vaizq/NutriDoser/Software/Sensei/src/wifi.hpp

#ifndef SERVER_HPP
#define SERVER_HPP

#include "esp_event.h"
#include "esp_log.h"
#include "esp_system.h"
#include "esp_wifi.h"
#include "freertos/FreeRTOS.h"
#include "freertos/event_groups.h"
#include "freertos/task.h"
#include "nvs_flash.h"
#include "wifi_provisioning/manager.h"
#include "wifi_provisioning/scheme_softap.h"
#include <string.h>

#include "lwip/err.h"
#include "lwip/sys.h"

#define ESP_WIFI_SAE_MODE WPA3_SAE_PWE_HUNT_AND_PECK
#define EXAMPLE_H2E_IDENTIFIER ""
#define ESP_WIFI_SCAN_AUTH_MODE_THRESHOLD WIFI_AUTH_WPA2_PSK
#define WIFI_MAXIMUM_RETRY 5

/* FreeRTOS event group to signal when we are connected*/
static EventGroupHandle_t wifi_event_group;

/* The event group allows multiple bits for each event, but we only care about
 * two events:
 * - we are connected to the AP with an IP
 * - we failed to connect after the maximum amount of retries */
#define WIFI_CONNECTED_BIT BIT0
#define WIFI_FAIL_BIT BIT1

static const char *TAG = "wifi station";

static int s_retry_num = 0;

static void event_handler(void *arg, esp_event_base_t event_base,
                          int32_t event_id, void *event_data) {
  if (event_base == WIFI_PROV_EVENT) {
    switch (event_id) {
    case WIFI_PROV_START:
      ESP_LOGI(TAG, "Provisioning started");
      break;
    case WIFI_PROV_CRED_RECV: {
      wifi_sta_config_t *wifi_sta_cfg = (wifi_sta_config_t *)event_data;
      ESP_LOGI(TAG,
               "Received Wi-Fi credentials"
               "\n\tSSID     : %s\n\tPassword : %s",
               (const char *)wifi_sta_cfg->ssid,
               (const char *)wifi_sta_cfg->password);
      break;
    }
    case WIFI_PROV_CRED_FAIL: {
      wifi_prov_sta_fail_reason_t *reason =
          (wifi_prov_sta_fail_reason_t *)event_data;
      ESP_LOGE(TAG,
               "Provisioning failed!\n\tReason : %s"
               "\n\tPlease reset to factory and retry provisioning",
               (*reason == WIFI_PROV_STA_AUTH_ERROR)
                   ? "Wi-Fi station authentication failed"
                   : "Wi-Fi access-point not found");
      break;
    }
    case WIFI_PROV_CRED_SUCCESS:
      ESP_LOGI(TAG, "provisioning successful");
      break;
    case WIFI_PROV_END:
      /* De-initialize manager once provisioning is finished */
      wifi_prov_mgr_deinit();
      break;
    default:
      break;
    }
  } else if (event_base == WIFI_EVENT) {
    if (event_id == WIFI_EVENT_STA_START) {
      esp_wifi_connect();
    } else if (event_id == WIFI_EVENT_STA_DISCONNECTED) {
      if (s_retry_num < WIFI_MAXIMUM_RETRY) {
        esp_wifi_connect();
        s_retry_num++;
        ESP_LOGI(TAG, "retry to connect to the AP");
      } else {
        xEventGroupSetBits(wifi_event_group, WIFI_FAIL_BIT);
      }
      ESP_LOGI(TAG, "connect to the AP fail");
    }
  } else if (event_base == IP_EVENT && event_id == IP_EVENT_STA_GOT_IP) {
    ip_event_got_ip_t *event = (ip_event_got_ip_t *)event_data;
    ESP_LOGI(TAG, "got ip:" IPSTR, IP2STR(&event->ip_info.ip));
    s_retry_num = 0;
    xEventGroupSetBits(wifi_event_group, WIFI_CONNECTED_BIT);
  }
}

void wifi_start_sta() {
  ESP_ERROR_CHECK(esp_wifi_set_mode(WIFI_MODE_STA));
  ESP_ERROR_CHECK(esp_wifi_start());
}

void wifi_init() {

  ESP_ERROR_CHECK(esp_netif_init());

  ESP_ERROR_CHECK(esp_event_loop_create_default());
  wifi_event_group = xEventGroupCreate();

  ESP_ERROR_CHECK(esp_event_handler_register(WIFI_PROV_EVENT, ESP_EVENT_ANY_ID,
                                             &event_handler, NULL));
  ESP_ERROR_CHECK(esp_event_handler_register(PROTOCOMM_SECURITY_SESSION_EVENT,
                                             ESP_EVENT_ANY_ID, &event_handler,
                                             NULL));
  ESP_ERROR_CHECK(esp_event_handler_register(WIFI_EVENT, ESP_EVENT_ANY_ID,
                                             &event_handler, NULL));
  ESP_ERROR_CHECK(esp_event_handler_register(IP_EVENT, IP_EVENT_STA_GOT_IP,
                                             &event_handler, NULL));

  esp_netif_create_default_wifi_sta();
  esp_netif_create_default_wifi_ap();

  wifi_init_config_t wifiConfig= WIFI_INIT_CONFIG_DEFAULT();
  ESP_ERROR_CHECK(esp_wifi_init(&wifiConfig));

  wifi_prov_mgr_config_t provConfig{
      .scheme = wifi_prov_scheme_softap,
      .scheme_event_handler = WIFI_PROV_EVENT_HANDLER_NONE,
  };

  ESP_ERROR_CHECK(wifi_prov_mgr_init(provConfig));

  bool provisioned;
  ESP_ERROR_CHECK(wifi_prov_mgr_is_provisioned(&provisioned));

  if (!provisioned) {
    ESP_LOGI(TAG, "start provisioning");
    ESP_ERROR_CHECK(wifi_prov_mgr_start_provisioning(WIFI_PROV_SECURITY_0, NULL,
                                                     "NutriDoser", NULL));
  } else {
    ESP_LOGI(TAG, "Already provisioned, starting Wi-Fi STA");
    wifi_prov_mgr_deinit();
    wifi_start_sta();
  }

  /* Waiting until either the connection is established (WIFI_CONNECTED_BIT) or
   * connection failed for the maximum number of re-tries (WIFI_FAIL_BIT). The
   * bits are set by event_handler() (see above) */
  EventBits_t bits =
      xEventGroupWaitBits(wifi_event_group, WIFI_CONNECTED_BIT | WIFI_FAIL_BIT,
                          pdFALSE, pdFALSE, portMAX_DELAY);

  /* xEventGroupWaitBits() returns the bits before the call returned, hence we
   * can test which event actually happened. */
  if (bits & WIFI_CONNECTED_BIT) {
    ESP_LOGI(TAG, "connected to WiFi");
    return;
  } else if (bits & WIFI_FAIL_BIT) {
    ESP_LOGI(TAG, "Failed to connect to WiFi");
  } else {
    ESP_LOGE(TAG, "UNEXPECTED EVENT");
  }
}

#endif
